qDave17/Stabilizator-de-Tensiune-cu-ERS/P1_2025_433C_Nedelea_David_Adrian_SERS_N19_Orcad/IMG_8656.png

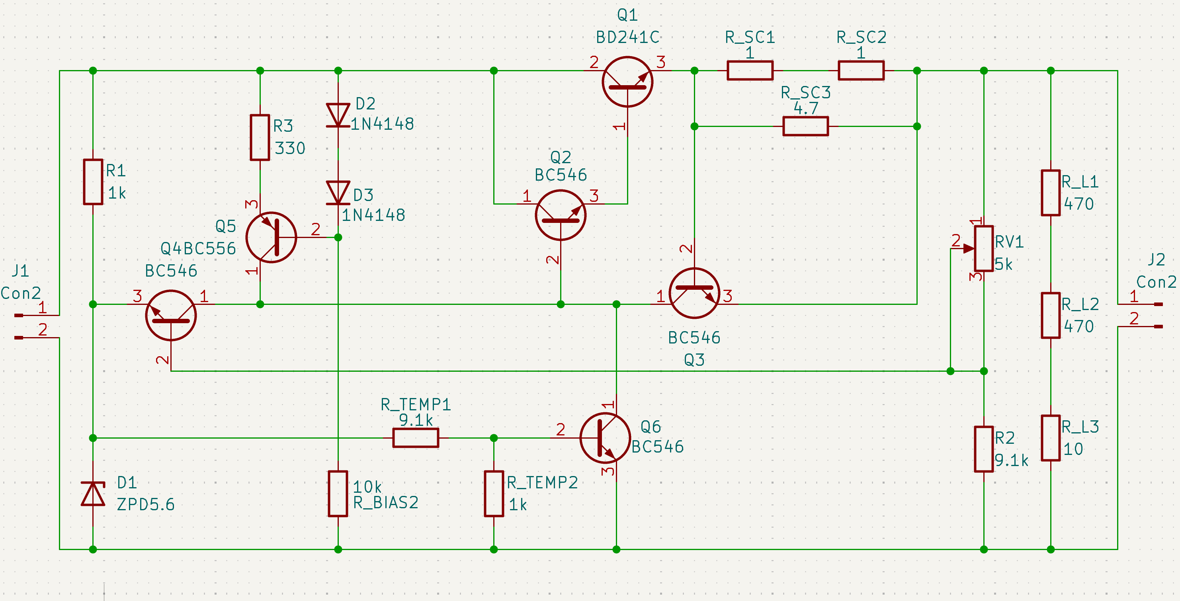
P1_2025_433C_Nedelea_David_Adrian_SERS_N19_Orcad/IMG_8656.png
